JKocher/LENR/Elmer-3a/Results/1MHz.PNG

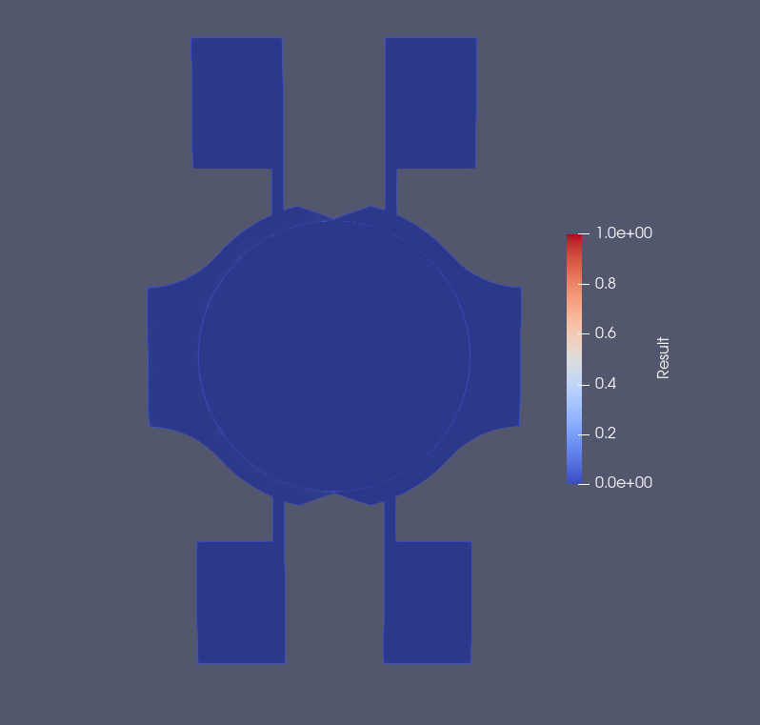
Elmer-3a/Results/1MHz.PNG
