JKocher/LENR/Elmer-3a/Results/20kHz.PNG

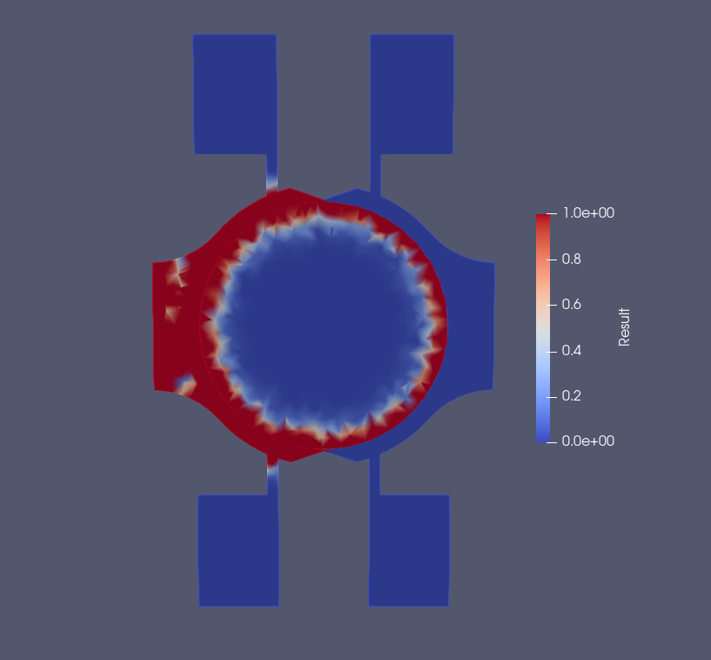
Elmer-3a/Results/20kHz.PNG
