JKocher/LENR/Elmer-3a/Results/30kHz.PNG

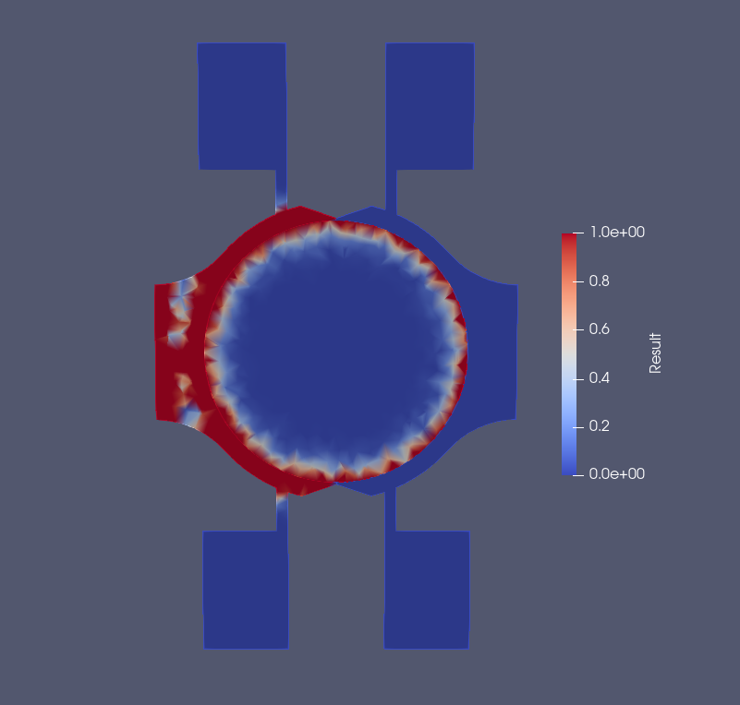
Elmer-3a/Results/30kHz.PNG
