JKocher/LENR/Elmer-3a/Results/40kHz.PNG

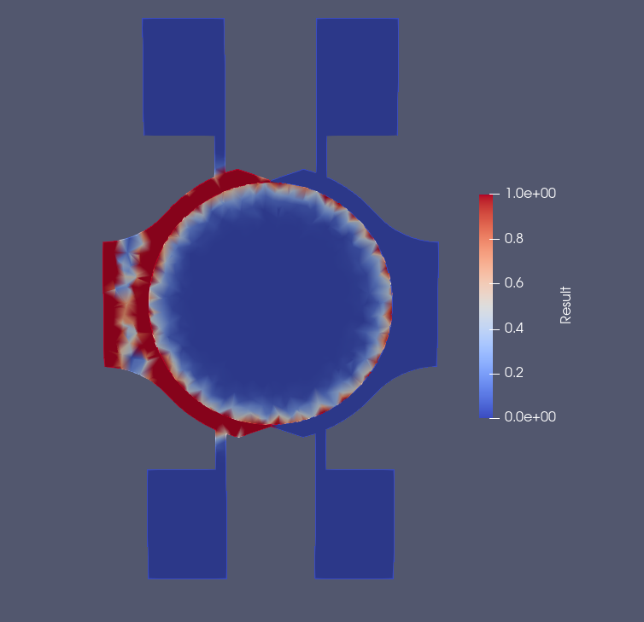
Elmer-3a/Results/40kHz.PNG
