JKocher/LENR/Elmer-3a/Results/50kHz.PNG

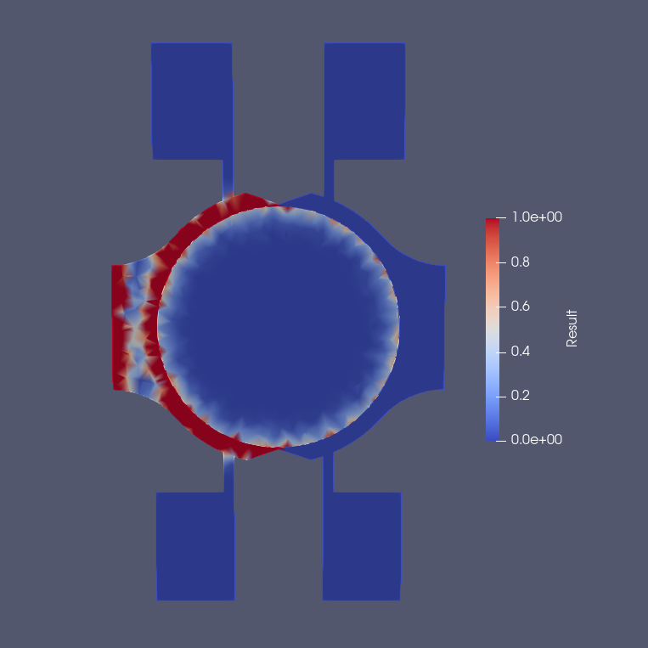
Elmer-3a/Results/50kHz.PNG
