JKocher/LENR/Elmer-3a/Results/70kHz.PNG

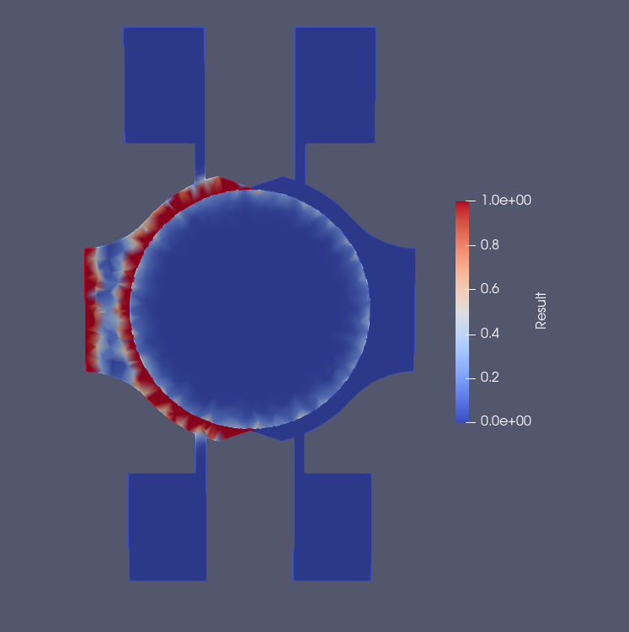
Elmer-3a/Results/70kHz.PNG
