JKocher/LENR/Elmer-3a/Results/80kHz.PNG

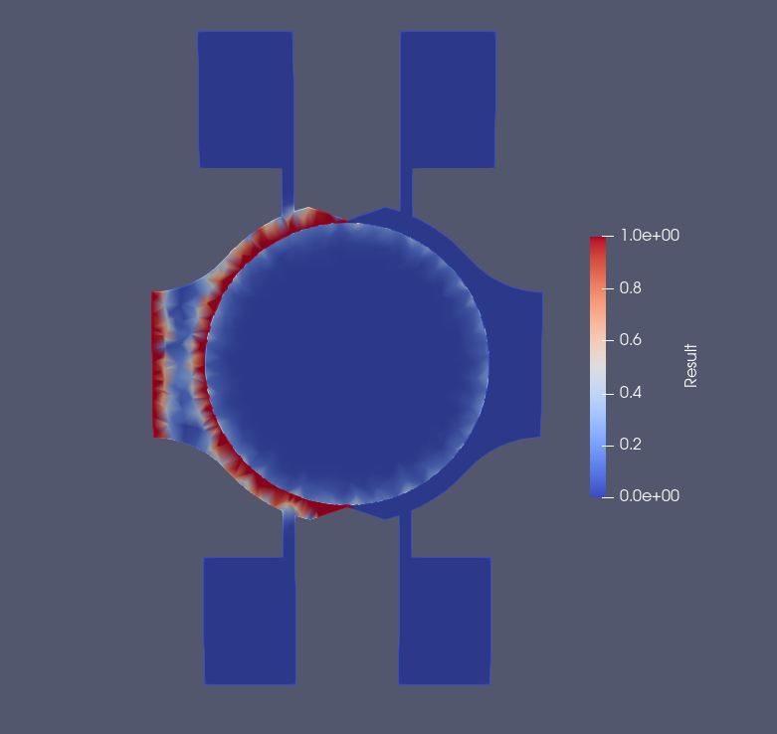
Elmer-3a/Results/80kHz.PNG
