JKocher/LENR/Elmer-3a/Results/90kHz.PNG

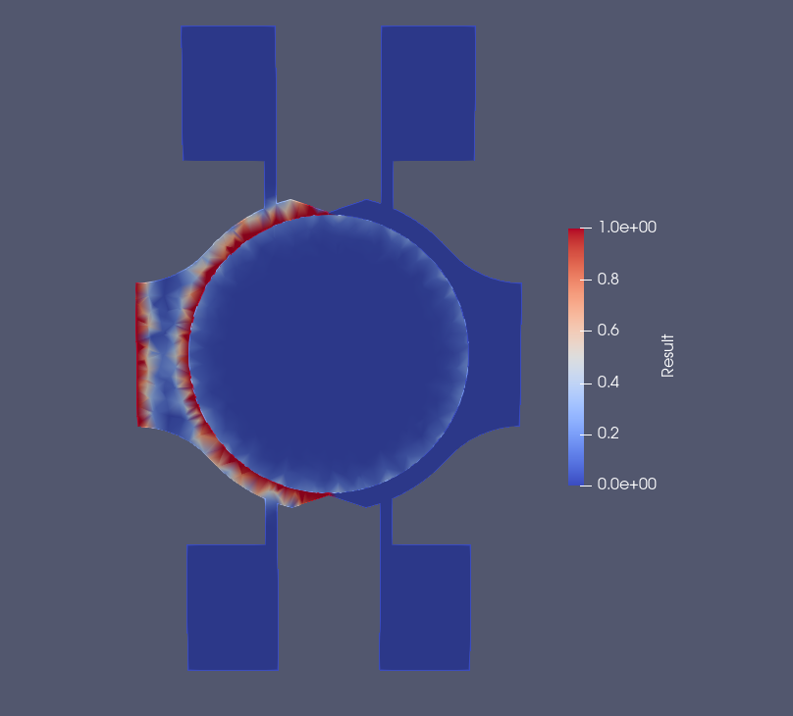
Elmer-3a/Results/90kHz.PNG
