JKocher/LENR/Elmer-3a/Results/100kHz.PNG

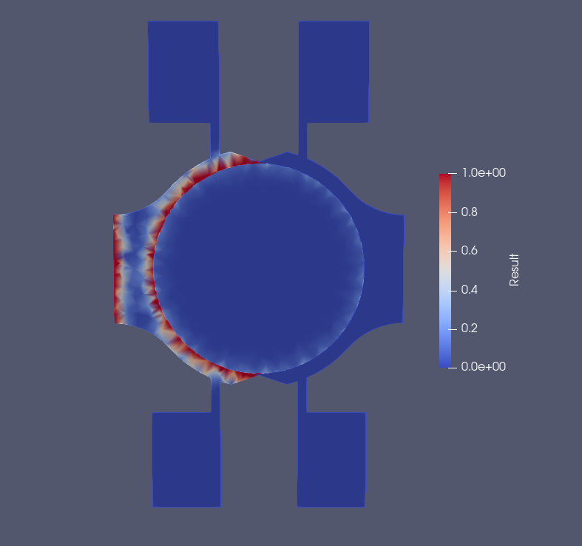
Elmer-3a/Results/100kHz.PNG
