JKocher/LENR/Elmer-3a/Results/110kHz.PNG

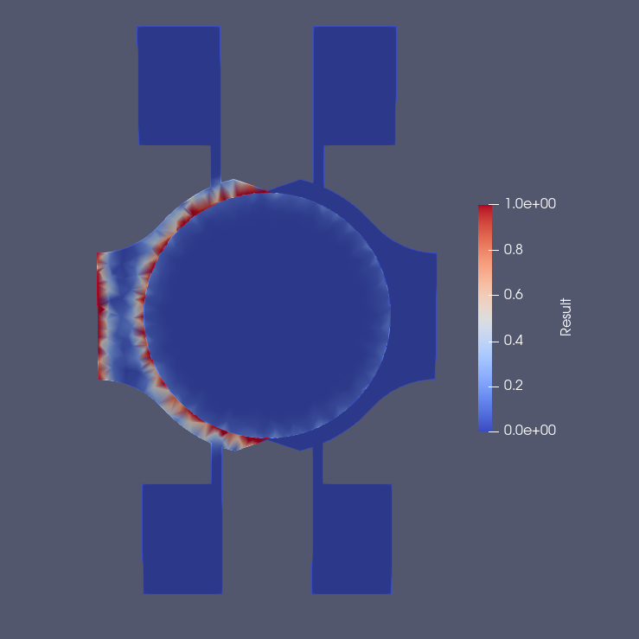
Elmer-3a/Results/110kHz.PNG
