JKocher/LENR/Elmer-3a/Results/Waveforms 20-110kHz.PNG

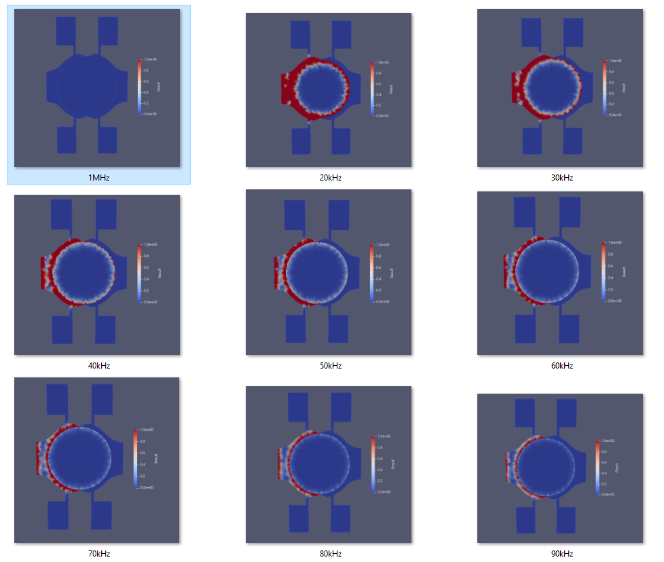
Elmer-3a/Results/Waveforms 20-110kHz.PNG
